maidstone-hackspace/qa-keypad/wemos-qa/wemos-qa.h

#ifndef wemos_config_H
#define wemos_config_H

#define API_STARTUP "http://ng.snapwire-portal.co.uk/api/StartUp"
#define API_POLL "http://ng.snapwire-portal.co.uk/api/Poll"
#define API_ANSWER "http://ng.snapwire-portal.co.uk/api/SubmitAnswer"

#define ONE_SECOND 1000

#endif
